joeostrander/consolized-game-boy/images/dmg_link_mount.JPG

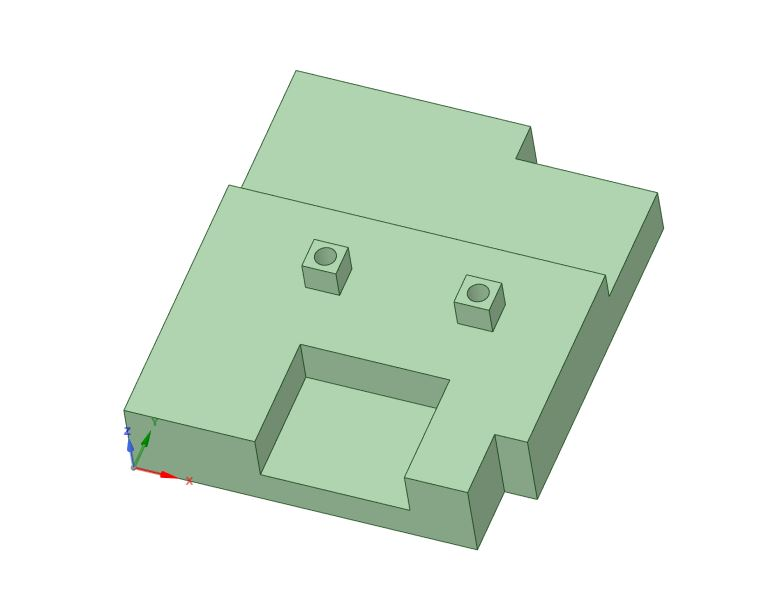
images/dmg_link_mount.JPG
