joeostrander/consolized-game-boy/images/screencap_osd.jpg

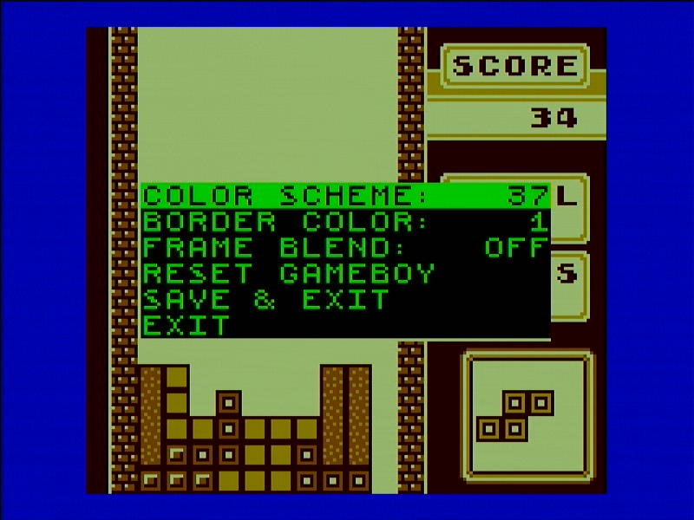
images/screencap_osd.jpg
