joeostrander/consolized-game-boy/images/SGBConsole_v3_2.jpg

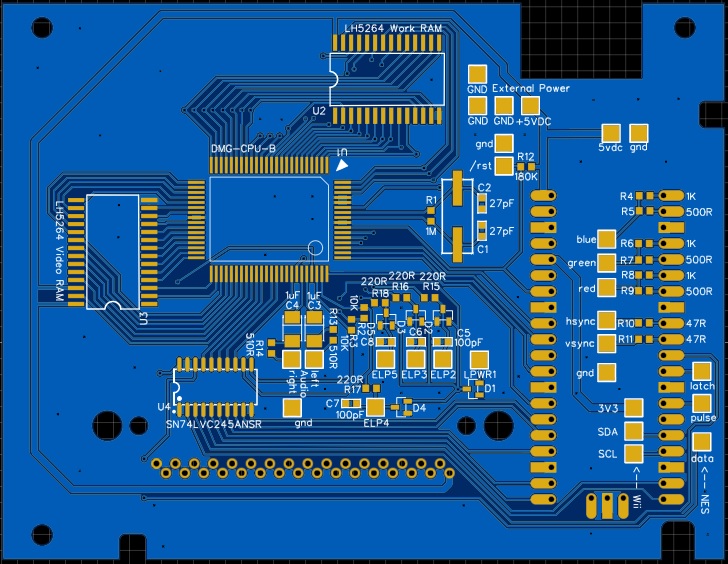
images/SGBConsole_v3_2.jpg
