joeostrander/consolized-game-boy/images/v3_2_back.jpg

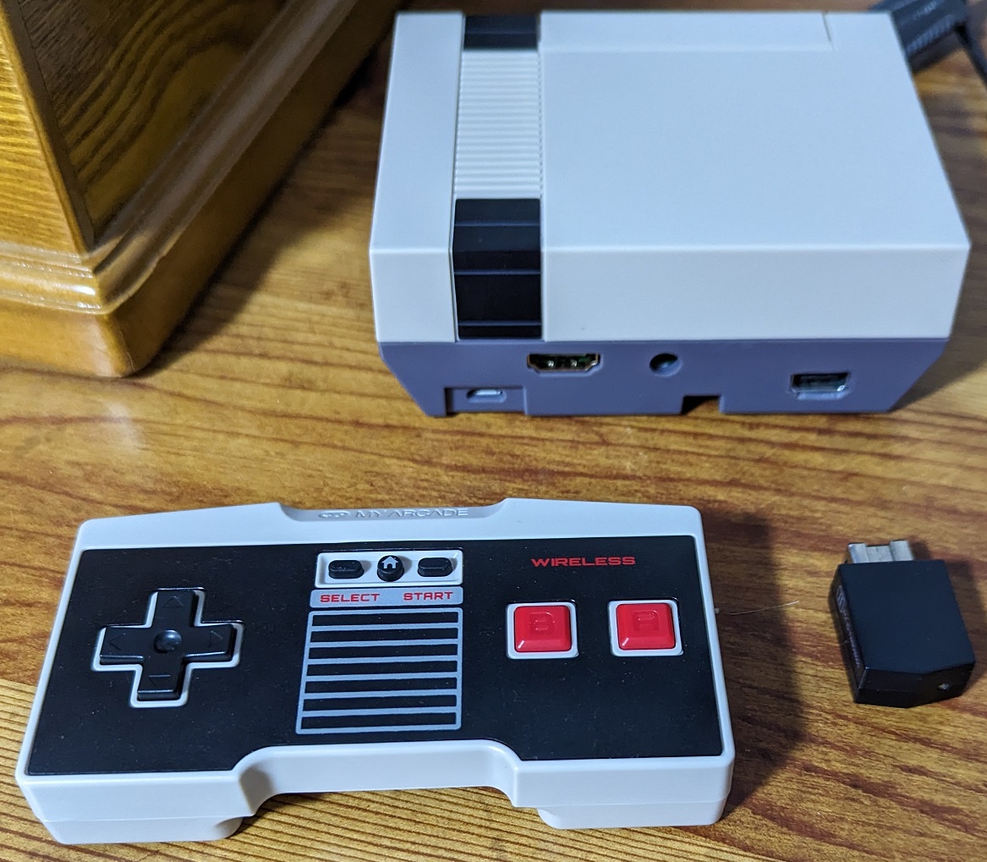
images/v3_2_back.jpg
