joeostrander/consolized-game-boy/images/v3_2_linked.jpg

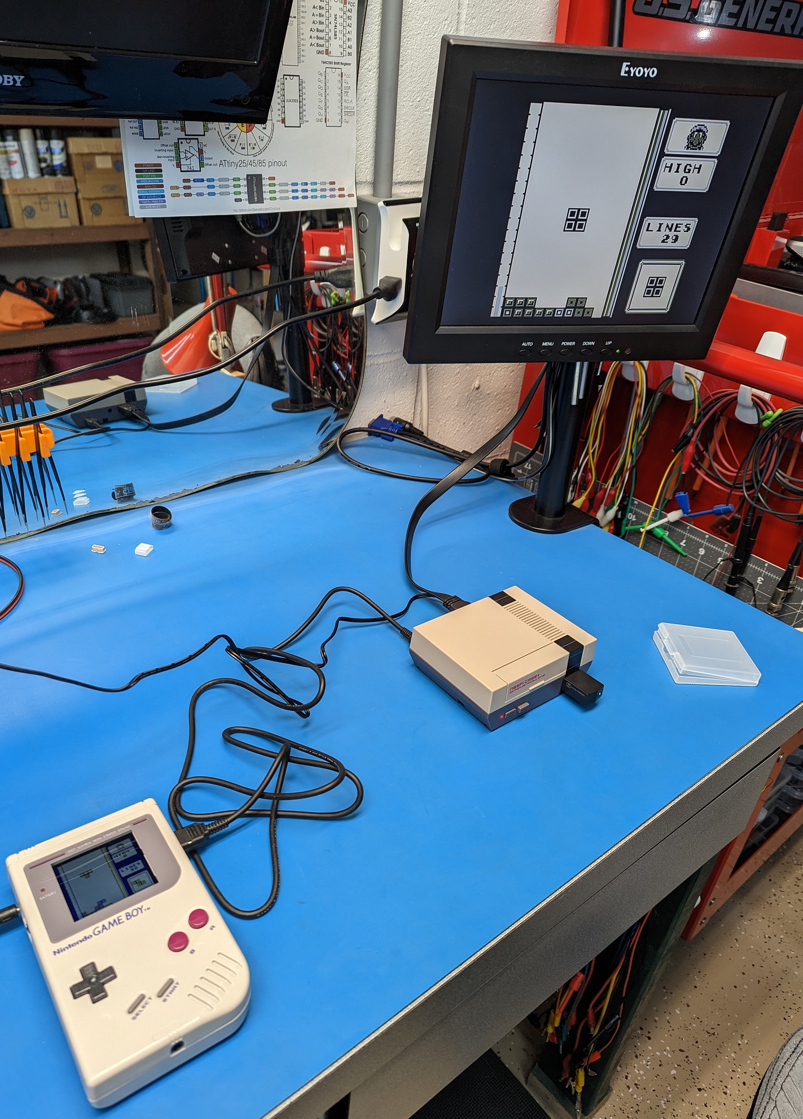
images/v3_2_linked.jpg
