joeostrander/consolized-game-boy/images/v3_2_lp4.jpg

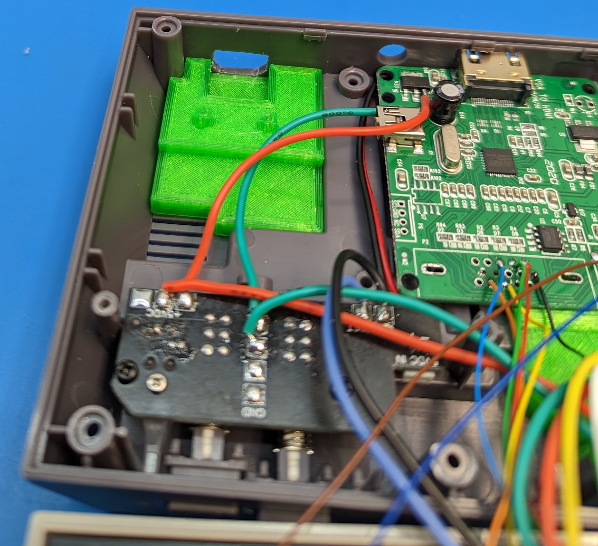
images/v3_2_lp4.jpg
