joeostrander/consolized-game-boy/images/v3_2_lp8.jpg

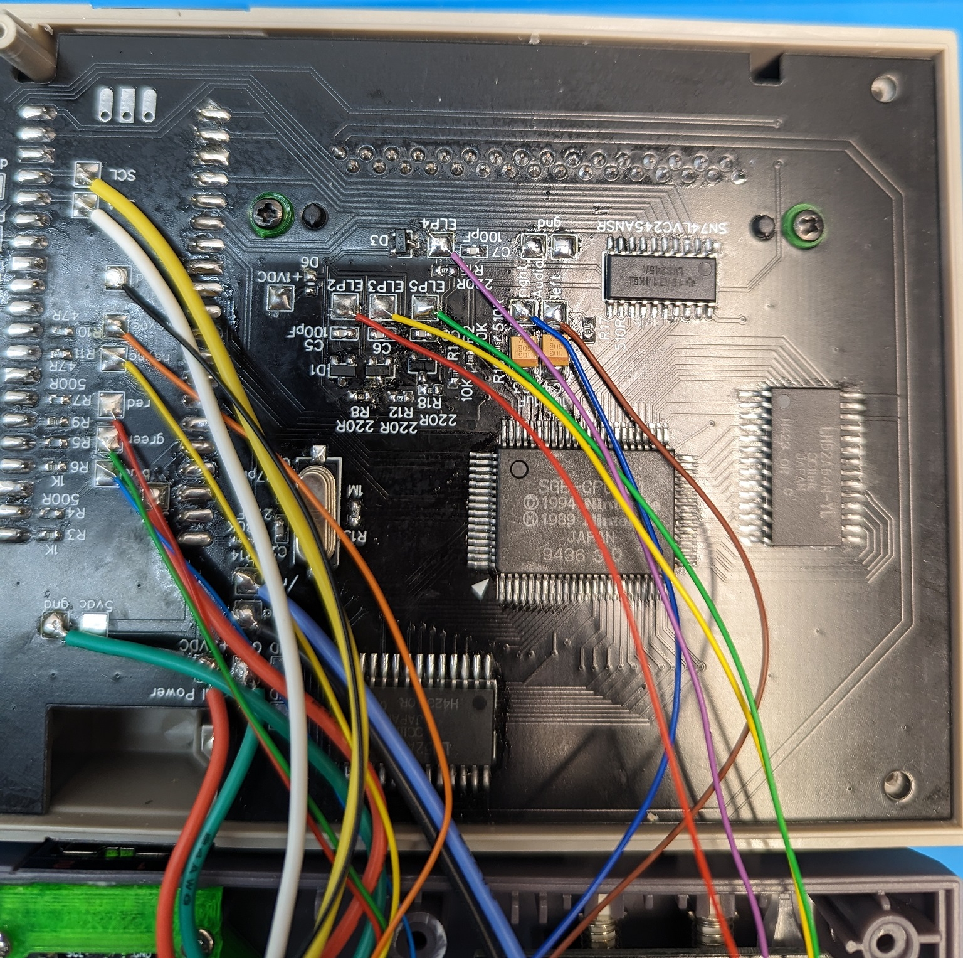
images/v3_2_lp8.jpg
