joeostrander/consolized-game-boy/images/v3_2_top_outside.jpg

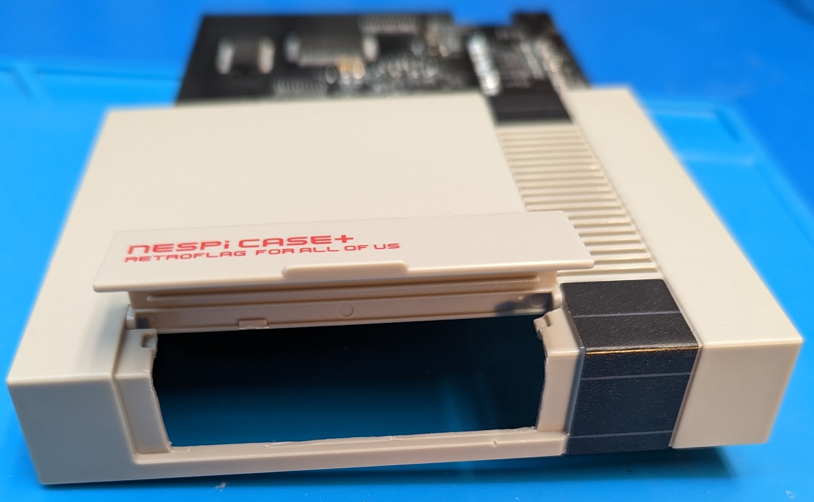
images/v3_2_top_outside.jpg
