joeostrander/consolized-game-boy/src/gb_vga/mario.h

#include <stdint.h>

// Mario splash screen in packed 2bpp format (4 pixels per byte)
static const uint8_t __attribute__((aligned(4))) mario_packed_160x144[] = {
0x00,0x00,0x00,0x00,0x00,0x00,0x00,0x00,0x00,0x00,0x00,0x00,0x00,0x00,0x00,0x00,
0x00,0x00,0x00,0x00,0x00,0x00,0x00,0x00,0x00,0x00,0x00,0x00,0x00,0x00,0x00,0x00,
0x00,0x00,0x00,0x00,0x00,0x00,0x00,0x00,0x30,0x3c,0x0f,0xf0,0x3f,0xf0,0x0f,0xf0,
0x0f,0xf0,0x00,0x00,0x0f,0xf0,0x0f,0xf0,0x00,0x00,0x00,0x00,0x30,0x3c,0x0f,0xf0,
0x3f,0xf0,0x3c,0x00,0x3f,0xf0,0x00,0x00,0x3f,0xfc,0x0f,0xf0,0x30,0x3c,0x3f,0xfc,
0x3c,0xfc,0x30,0xfc,0x3c,0x3c,0x03,0xc0,0x3c,0x3c,0x30,0x30,0x3c,0x3c,0x30,0xfc,
0x00,0x00,0x00,0x00,0x30,0x3c,0x3c,0x3c,0x3c,0x3c,0x3c,0x00,0x30,0xfc,0x00,0x00,
0x03,0xc0,0x03,0xc0,0x3c,0xfc,0x3c,0x00,0x3f,0xfc,0x30,0xfc,0x3c,0x3c,0x03,0xc0,
0x3c,0x3c,0x0c,0xc0,0x3c,0x3c,0x00,0xfc,0x00,0x00,0x00,0x00,0x33,0x3c,0x3c,0x3c,
0x3c,0x3c,0x3c,0x00,0x30,0xfc,0x00,0x00,0x03,0xc0,0x03,0xc0,0x3f,0xfc,0x3f,0xf0,
0x33,0x3c,0x3f,0xfc,0x3f,0xf0,0x03,0xc0,0x3c,0x3c,0x03,0x00,0x3c,0x3c,0x0f,0xf0,
0x00,0x00,0x00,0x00,0x3f,0xfc,0x3c,0x3c,0x3f,0xf0,0x3c,0x00,0x30,0xfc,0x00,0x00,
0x03,0xc0,0x03,0xc0,0x33,0x3c,0x3c,0x00,0x30,0x3c,0x30,0xfc,0x3c,0xc0,0x03,0xc0,
0x3c,0x3c,0x0c,0xc0,0x3c,0x3c,0x3f,0x00,0x00,0x00,0x00,0x00,0x3c,0xfc,0x3c,0x3c,
0x3c,0xc0,0x3c,0x00,0x30,0xfc,0x00,0x00,0x03,0xc0,0x03,0xc0,0x30,0x3c,0x3c,0x00,
0x30,0x3c,0x30,0xfc,0x3c,0x3c,0x0f,0xf0,0x0f,0xf0,0x30,0x30,0x0f,0xf0,0x3f,0xfc,
0x00,0x00,0x00,0x00,0x30,0x3c,0x0f,0xf0,0x3c,0x3c,0x3f,0xfc,0x3f,0xf0,0x00,0x00,
0x03,0xc0,0x0f,0xf0,0x30,0x3c,0x3f,0xfc,0x00,0x00,0x00,0x00,0x00,0x00,0x00,0x00,
0x00,0x00,0x00,0x00,0x00,0x00,0x00,0x00,0x00,0x00,0x00,0x00,0x00,0x00,0x00,0x00,
0x00,0x00,0x00,0x00,0x00,0x00,0x00,0x00,0x00,0x00,0x00,0x00,0x00,0x00,0x00,0x00,
0x00,0x00,0x00,0x00,0x00,0x00,0x00,0x00,0x00,0x00,0x00,0x00,0x00,0x00,0x0f,0xc0,
0x00,0x00,0x00,0x00,0x00,0x00,0x00,0x00,0x00,0x00,0x00,0x00,0x00,0x00,0x00,0x00,
0x00,0x00,0x00,0x00,0x00,0x00,0x00,0x00,0x00,0x00,0x00,0x00,0x00,0x00,0x00,0x00,
0x00,0x00,0x0f,0xf0,0x00,0x00,0x35,0x70,0x00,0x00,0x0f,0xf0,0x0f,0xf0,0x00,0x00,
0x03,0xc0,0x00,0x00,0x03,0xc0,0x00,0x00,0x00,0x00,0x0f,0xf0,0x0f,0xf0,0x0f,0xf0,
0x00,0x00,0x00,0x00,0x00,0x00,0x00,0x00,0x00,0x00,0x3c,0x3c,0x00,0x00,0xd4,0x5c,
0x30,0x30,0x3c,0x3c,0x3c,0x3c,0x00,0x00,0x0f,0xc0,0x00,0x00,0x0f,0xc0,0x00,0x00,
0x00,0x00,0x3c,0xf0,0x3c,0x3c,0x3c,0x3c,0x00,0x00,0x00,0x00,0x00,0x00,0x00,0x00,
0x00,0x00,0x3c,0x3c,0x00,0x00,0xd0,0xdc,0x0c,0xc0,0x3c,0x3c,0x3c,0x3c,0x00,0x00,
0x03,0xc0,0x0f,0xf0,0x03,0xc0,0x00,0x00,0x00,0x00,0x30,0xf0,0x3c,0x3c,0x3c,0x3c,
0x00,0x00,0x00,0x00,0x00,0x00,0x00,0x00,0x00,0x00,0x3c,0x3c,0x00,0x00,0xd0,0xdc,
0x03,0x00,0x3c,0x3c,0x3c,0x3c,0x00,0x00,0x03,0xc0,0x0f,0xf0,0x03,0xc0,0x00,0x00,
0x00,0x00,0x30,0xfc,0x3c,0x3c,0x3c,0x3c,0x00,0x00,0x00,0x00,0x00,0x00,0x00,0x00,
0x00,0x00,0x3c,0x3c,0x00,0x00,0xd7,0x5c,0x0c,0xc0,0x3c,0x3c,0x3c,0x3c,0x00,0x00,
0x03,0xc0,0x00,0x00,0x03,0xc0,0x00,0x00,0x00,0x00,0x3f,0xfc,0x3c,0x3c,0x3c,0x3c,
0x00,0x00,0x00,0x00,0x00,0x00,0x00,0x00,0x00,0x00,0x0f,0xf0,0x00,0x00,0x35,0x70,
0x30,0x30,0x0f,0xf0,0x0f,0xf0,0x00,0x00,0x0f,0xf0,0x00,0x00,0x0f,0xf0,0x00,0x00,
0x00,0x00,0x00,0xf0,0x0f,0xf0,0x0f,0xf0,0x00,0x00,0x00,0x00,0x00,0x00,0x00,0x00,
0x00,0x00,0x00,0x00,0x00,0x00,0x0f,0xc0,0x00,0x00,0x00,0x00,0x00,0x00,0x00,0x00,
0x00,0x00,0x00,0x00,0x00,0x00,0x00,0x00,0x00,0x00,0x00,0x00,0x00,0x00,0x00,0x00,
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
};
